Totof34/Preamp_micro_USB/images/Box2.JPG

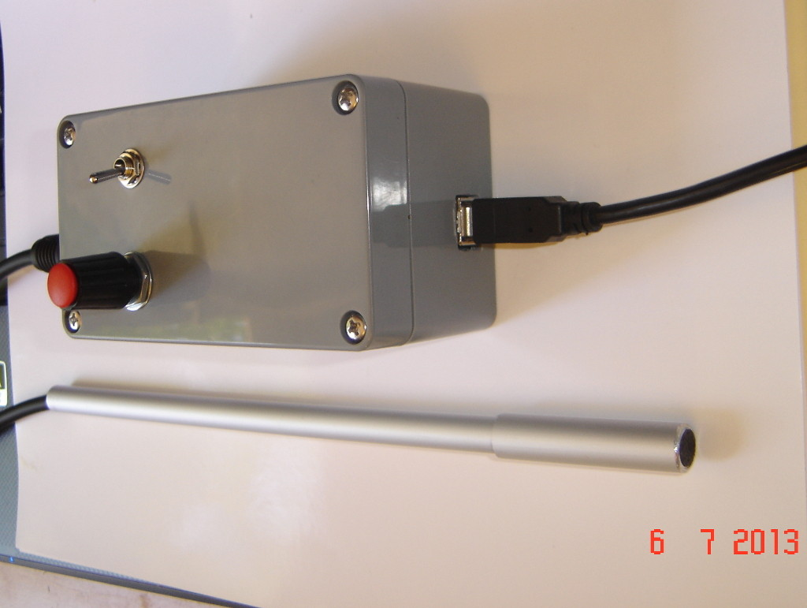
images/Box2.JPG
