Totof34/Preamp_micro_USB/images/PCM2904_PCB.png

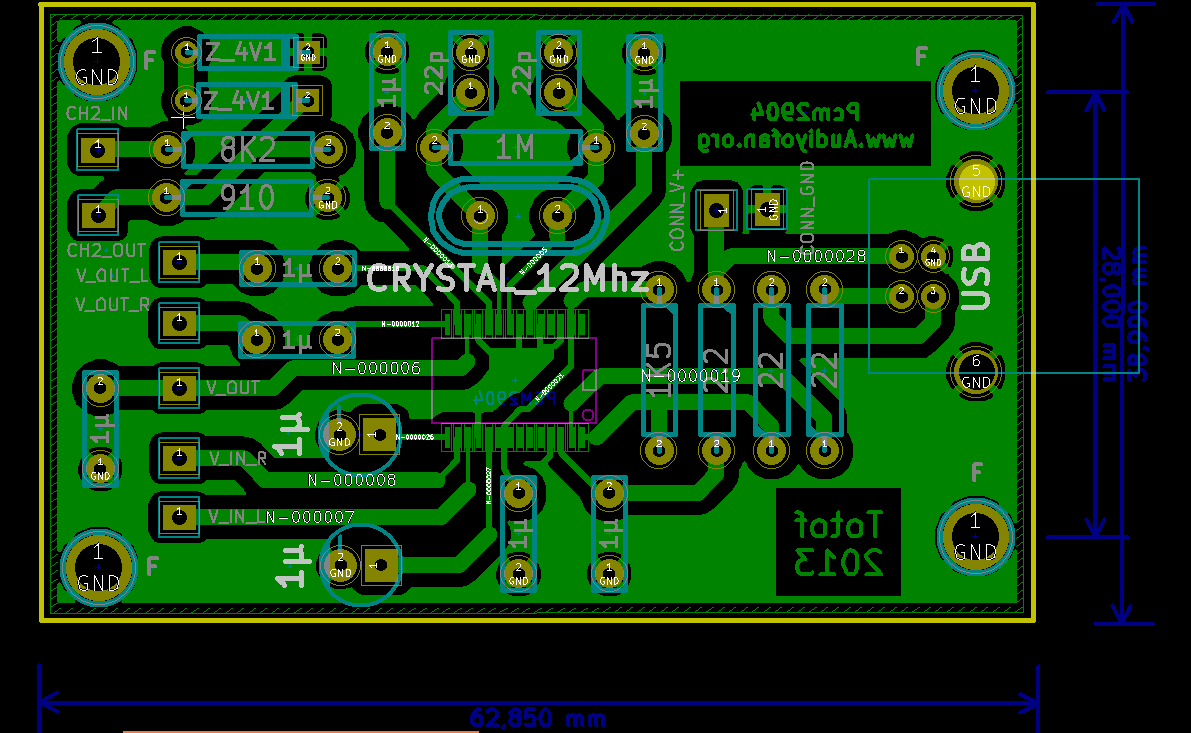
images/PCM2904_PCB.png
