Totof34/Preamp_micro_USB/images/Preamp_micro_3D.png

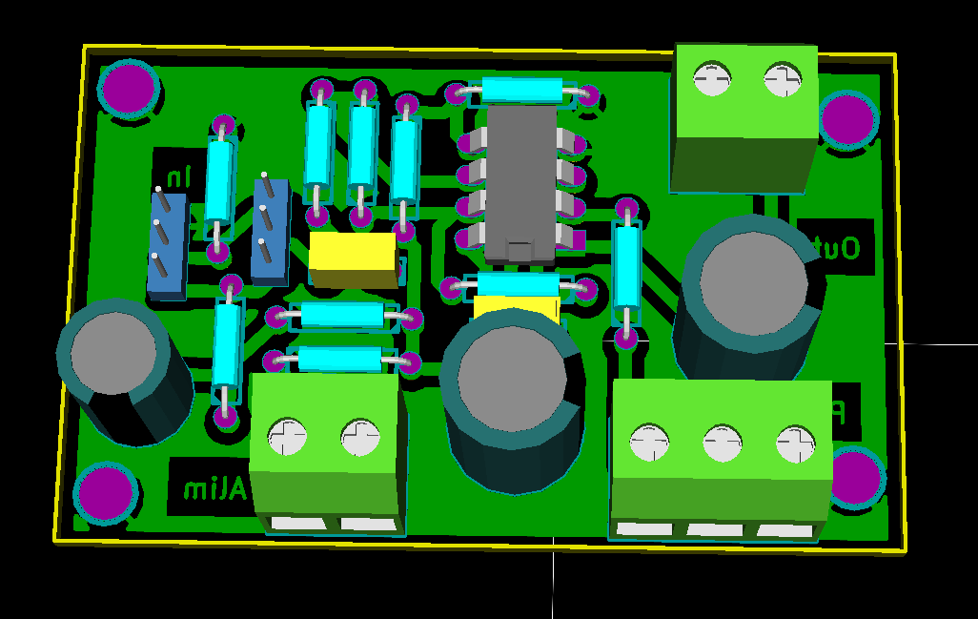
images/Preamp_micro_3D.png
